AdelStudent/Codepo_22_23/projet codepo/courant_HTSL/courant_HTSL.ino

// AC & DC Current Sensor with LCD By Solarduino

// Note Summary
// Note :  Safety is very important when dealing with electricity. We take no responsibilities while you do it at your own risk.
// Note :  This AC & DC  Current Sensor Code is for HSTS016L Hall effect split core current transformer use.
// Note :  The value shown in Serial Monitor / LCD Display is refreshed every second and measurement value is the average value of 4000 sample readings for nearly a second.
// Note :  The current measured is the Root Mean Square (RMS) value.
// Note :  The analog value per sample is squared and accumulated for every 4000 samples before being averaged. The averaged value is then getting square-rooted.
// Note :  The unit provides reasonable accuracy and may not be comparable with other expensive branded and commercial product.
// Note :  All credit shall be given to Solarduino.

/*/////////////////////////////////////////////////////////////////////////////////////////////////////////////////////////////////////////////////////////////////////////////////////*/////////////*/

/* 0- General */

int decimalPrecision = 2;                   // decimal places for all values shown in LED Display & Serial Monitor

/* 1- AC Current Measurement */

int currentAnalogInputPin = A1;             // Which pin to measure Current Value (A0 is reserved for LCD Display Shield Button function)
int calibrationPin = A2;                    // Which pin to calibrate offset middle value
float manualOffset = 0.045;                  // Key in value to manually offset the initial value
float mVperAmpValue = 20.83;                 // If using "Hall-Effect" Current Transformer, key in value using this formula: mVperAmp = maximum voltage range (in milli volt) / current rating of CT
// For example, a 20A Hall-Effect Current Transformer rated at 20A, 2.5V +/- 0.625V, mVperAmp will be 625 mV / 20A = 31.25mV/A
// For example, a 30A Hall-Effect Current Transformer rated at 50A, 2.5V +/- 0.625V, mVperAmp will be 625 mV / 30A = 20.83333 mV/A
float supplyVoltage = 3300;                 // Analog input pin maximum supply voltage, Arduino Uno or Mega is 5000mV while Arduino due is 3300mV
float offsetSampleRead = 0;                 /* to read the value of a sample for offset purpose later */
float currentSampleRead  = 0;               /* to read the value of a sample including currentOffset1 value*/
float currentLastSample  = 0;               /* to count time for each sample. Technically 1 milli second 1 sample is taken */
float currentSampleSum   = 0;               /* accumulation of sample readings */
float currentSampleCount = 0;               /* to count number of sample. */
float currentMean ;                         /* to calculate the average value from all samples, in analog values*/
float RMSCurrentMean ;                      /* square roof of currentMean, in analog values */
float FinalRMSCurrent ;                     /* the final RMS current reading*/


void setup()                                              /*codes to run once */
{
  Serial.begin(9600);                               /* to display readings in Serial Monitor at 9600 baud rates */
}


void loop()                                                                                                   /*codes to run again and again */
{
  /* 1- AC & DC Current Measurement */

  if (micros() >= currentLastSample + 200)                                                              /* every 0.2 milli second taking 1 reading */
  {
    currentSampleRead = analogRead(currentAnalogInputPin) - analogRead(calibrationPin);  /* read the sample value including offset value*/
    currentSampleSum = currentSampleSum + sq(currentSampleRead) ;                                      /* accumulate total analog values for each sample readings*/
    currentSampleCount = currentSampleCount + 1;                                                       /* to count and move on to the next following count */
    currentLastSample = micros();                                                                      /* to reset the time again so that next cycle can start again*/
  }

  if (currentSampleCount == 4000)                                                                       /* after 4000 count or 800 milli seconds (0.8 second), do this following codes*/
  {
    currentMean = currentSampleSum / currentSampleCount;                                              /* average accumulated analog values*/
    RMSCurrentMean = sqrt(currentMean);                                                               /* square root of the average value*/
    FinalRMSCurrent = (((RMSCurrentMean / 1023) * supplyVoltage) / mVperAmpValue) + manualOffset;     /* calculate the final RMS current*/
    if ((FinalRMSCurrent <= (625 / mVperAmpValue / 100)) or  (FinalRMSCurrent >30))                                         /* if the current detected is less than or up to 1%, set current value to 0A (0,3)*/
    {
      FinalRMSCurrent = 0;
    }
    Serial.print(" The Current RMS value is: ");
    Serial.print(FinalRMSCurrent, decimalPrecision);
    Serial.println(" A ");
    currentSampleSum = 0;                                                                             /* to reset accumulate sample values for the next cycle */
    currentSampleCount = 0;                                                                           /* to reset number of sample for the next cycle */
  }
}
