AdelStudent/Codepo_22_23/main/arduino_thingstream.ino

/*
Pour la personne qui va lire ce code:
    -Le module Thingstream Click est un micro-controlleur capable d'envoyer des mails via le Broker du 
      même nom.
    -Pour l'envoie de mail, il faut subscribe le Click au même topic que le "Flows" du site web, ici TEST1.
      Un fois, Click et Flows subscibed au bon topic, le Click n'a qu'à envoyer un message via publish_message().
    -Le module thingstream click utilise les pin Rx1/Tx1 pour communiquer (par extension =>Serial1). Attention,
      afin de communiquer, Arduino et Click doivent avoir le même GRD.
*/

//___________SETUP

int initThingstream(int *flag_init) {
  *flag_init = 0;
  delay(10000); // wait for the modem to initialize
  if (*flag_init == 0 ){
    LCD_print_IP("Waiting Server..");
    // ERROR : reset the Thingstream click
    Serial.println("DEBUG");
    Serial1.println("AT+IOTDEBUG=0");
    if(checkReception() == 1) {
        *flag_init = 1; 
        Serial.println("Debug : success");
      } else {
        Serial.println("Debug : fail");
      }
  }
  if(*flag_init == 1){
    LCD_print_IP("Waiting Server..");
    Serial.println("CREATE");
    Serial1.println("AT+IOTCREATE");  
    if(checkReception() == 1) { 
        *flag_init = 2; 
        Serial.println("Create : success");
     } else {
        Serial.println("Create : fail");
     }
  }
  if(*flag_init == 2){
    LCD_print_IP("Waiting Server..");
    Serial.println("CONNECT");
    Serial1.println("AT+IOTCONNECT=true");
    //Serial1.println("AT+IOTCONNECT=true,1440");
    if(checkReception() == 1) { 
        *flag_init = 3; 
        Serial.println("Connect : success");
    } else {
        Serial.println("Connect : fail");
    }
  }
  if(*flag_init == 3) {
    LCD_print_IP("Waiting Server..");
    Serial.println("SUBSCRIBE");
    Serial1.println("AT+IOTSUBSCRIBE=\"TEST1\",1");
    if(checkReception() == 1) { 
        *flag_init = 4; 
        Serial.println("Subscribe : success");
    } else {
        Serial.println("Subscribe : fail");
    }
  }
  //publish_message("TESTOTEST",flag_init); //Fonction permettant d'envoyer des messages au topic TEST1
}
//____________________________USEFULL FUNCTIONS_______________________//

//___________Sending Messages
void publish_message(char* msg,int *flag_init){
  if(*flag_init==4){
    char message[10000] = "\0";
    char message_to_send[500];
    sprintf(message_to_send, "AT+IOTPUBLISH=\"TEST1\",1,\"%s\"", msg);
    strcat(message, message_to_send);

    Serial.print("message : ");Serial.println(message); 
    Serial1.println(message);//COMMUNICATION to Thingstream
  }else{
    Serial.println("Thingstream Error : initThingstream didn't end well");
  }
}
int checkReception() {
  unsigned long timeInit = millis()*0.001;
  char message[150];
  int count = 0;

  while(true) {
    // If maximum time (20s) to wait for message reception exceeded
    if(millis()*0.001 - timeInit > 30.0) { 
      Serial.println("To Long Time");
      return 0;
     }
    // If not yet exceeded
    //Serial.println(Serial1.available());
    //delay(500);
    
    if (Serial1.available()){
        char st = Serial1.read();
        message[count] = st;  
        message[count+1] = '\0';  
        count += 1;
        
        if(message[count-1] == '\n'){
          Serial.print("Le message recu : ");          
          Serial.print(String(message));  //Affiche le message recu
          if (analyse(message) ==  1) {
            return 1;
          } else {
            return 0;
          }
        }
     }
  }
}
int analyse(String st) {
  // Arret de la publication si le mot STOP est reçu par le Click

  //Serial.println("Analyse has been called");
  int res = 1;  
  if(st.indexOf("GO") > 0 || st.indexOf("SUCCESS") > 0) {
    res = 1;
  } else {
    res = 0;
  }
  return res;
}

//___________Warning Messages
void publish_temperature_warning(float temperature,int *flag_init){
  char my_msg[500];
  sprintf(my_msg, "ERROR, température des batteries est de : %f.", temperature);
  publish_message(my_msg,flag_init);
  memset(my_msg, 0, sizeof(my_msg));

  checkReception(); //Cela permet de nettoyer le SerialPort ET de debugger si l'envoie du message a été un SUCCESS
}
void publish_SOC_warning(double SOC_lvl,int *flag_init){
  char my_msg[500];
  sprintf(my_msg, "ERROR, L'etat de charge des batteries est de : %lf.", SOC_lvl);
  publish_message(my_msg,flag_init);
  memset(my_msg, 0, sizeof(my_msg));

  checkReception(); //Cela permet de nettoyer le SerialPort ET de debugger si l'envoie du message a été un SUCCESS
}
void publish_current_warning(double output_pack_bat_current,int *flag_init){
  char my_msg[500];
  sprintf(my_msg, "ERROR, Le courant de sortie des batteries est de : %lf.", output_pack_bat_current);
  publish_message(my_msg,flag_init);
  memset(my_msg, 0, sizeof(my_msg));

  checkReception(); //Cela permet de nettoyer le SerialPort ET de debugger si l'envoie du message a été un SUCCESS
}
void publish_voltage_warning(float battery_voltage,int *flag_init){
  char my_msg[500];
  sprintf(my_msg, "ERROR, La tension de sur le pack batteries est de : %f.", battery_voltage);
  publish_message(my_msg,flag_init);
  memset(my_msg, 0, sizeof(my_msg));

  checkReception(); //Cela permet de nettoyer le SerialPort ET de debugger si l'envoie du message a été un SUCCESS
}


//____________________________TEST FUNCTIONS_______________________//
int ask_info_thingstream() {
  delay(1000); // wait for the modem to initialize

  // ERROR : reset the Thingstream click
  Serial.println("Asking Info to Thingstream");
  Serial1.println("AT+IOTINFO");
  checkReception();
}
void connectivity_test_thingstream(){
  delay(1000); // wait for the modem to initialize

  // ERROR : reset the Thingstream click
  Serial.println("Connectivity Thingstream Test");
  Serial1.println("AT+IOTTEST");
  if(checkReception() == 1) { 
      Serial.println("Test : success");
  } else {
    Serial.println("Connectivity Test : fail");
  }
}

void reset_thingstream(){
  delay(1000); // wait for the modem to initialize

  // ERROR : reset the Thingstream click
  Serial.println("Reset Thingstream");
  Serial1.println("AT+IOTDESTROY");
  if(checkReception() == 1) { 
      Serial.println("Test : success");
  } else {
    Serial.println("Reset Test : fail");
  }
}
