AdelStudent/Codepo_22_23/esp32_easy/setup_ESP.ino

//____________________________SETUP_Function_____________________________//
void setup_ESP32(){

  //-----------------WIFI-------------------
  setup_wifi();
  //-----------------SPIFFS-----------------
  setup_SPIFFS();
  //-----------------SERVER-----------------
  setup_asynch_server();
  //-----------------DATE-------------------
  setup_ESP32_time();
}
